pu2clr/Si4825_RADIO_HACK/Images/band_selector_prototype_01.jpg

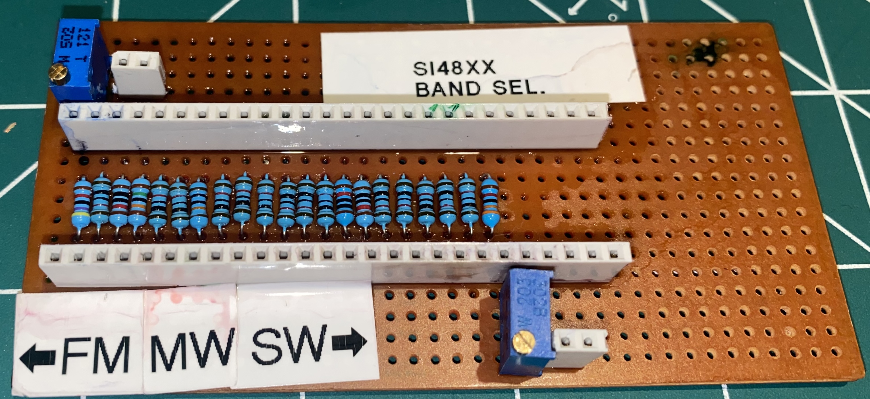
Images/band_selector_prototype_01.jpg
