pu2clr/Si4825_RADIO_HACK/Images/R_EXAMPLE_01.jpg

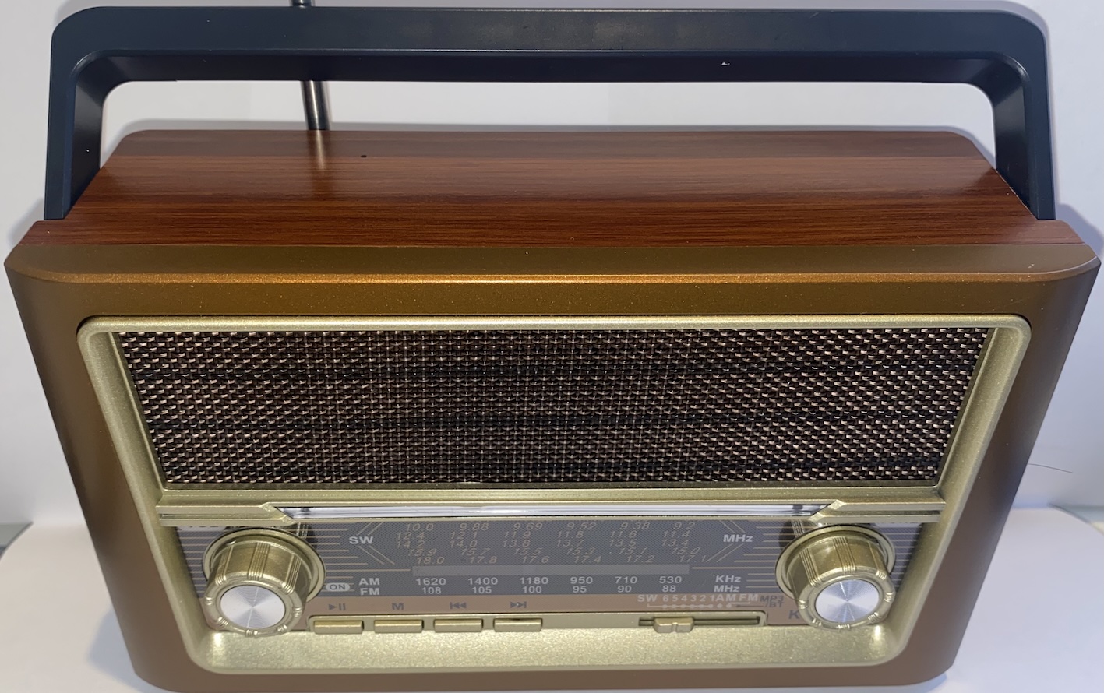
Images/R_EXAMPLE_01.jpg
