pu2clr/Si4825_RADIO_HACK/Images/R_EXAMPLE_02.jpg

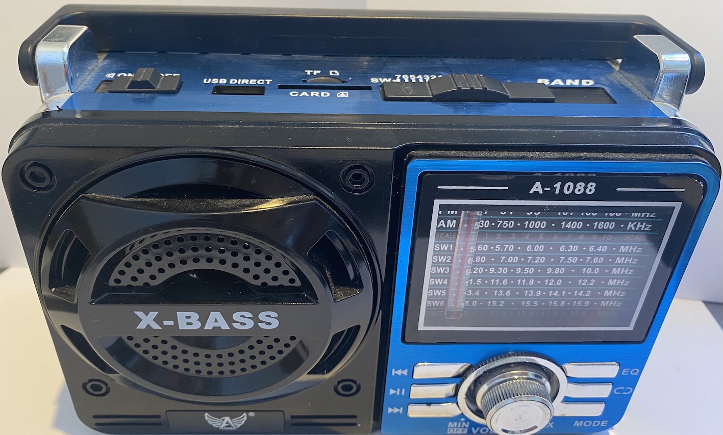
Images/R_EXAMPLE_02.jpg
