pu2clr/Si4825_RADIO_HACK/Images/SI4824A20.jpg

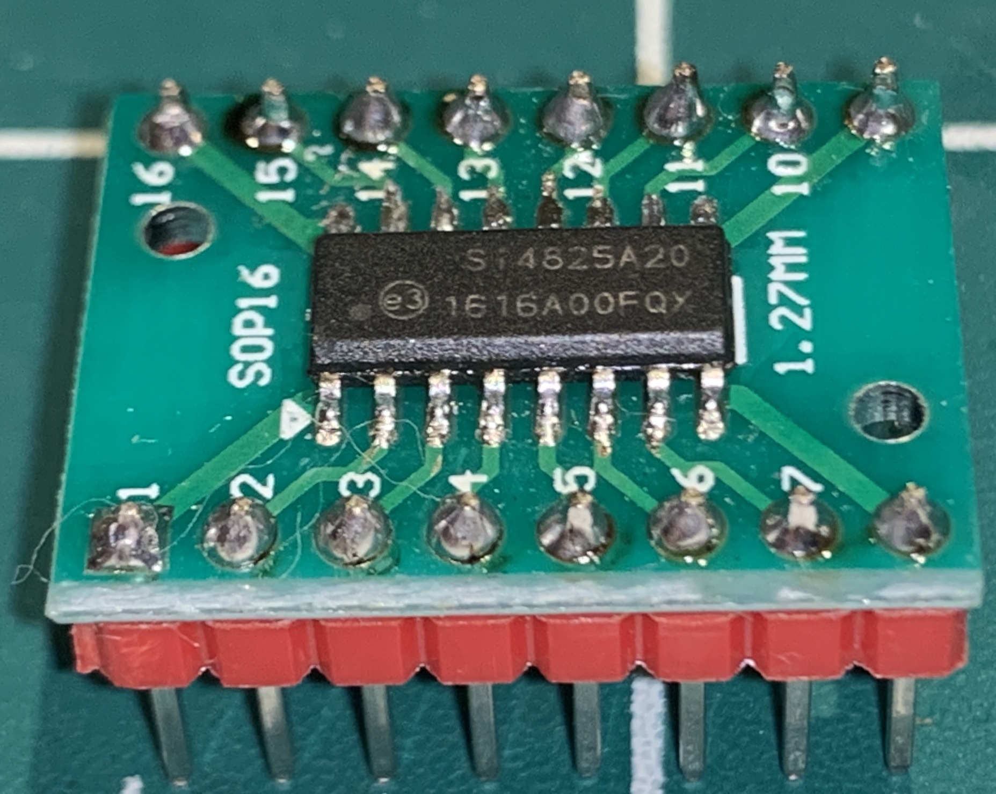
Images/SI4824A20.jpg
