pu2clr/Si4825_RADIO_HACK/schematic/SI4825_APP.jpg

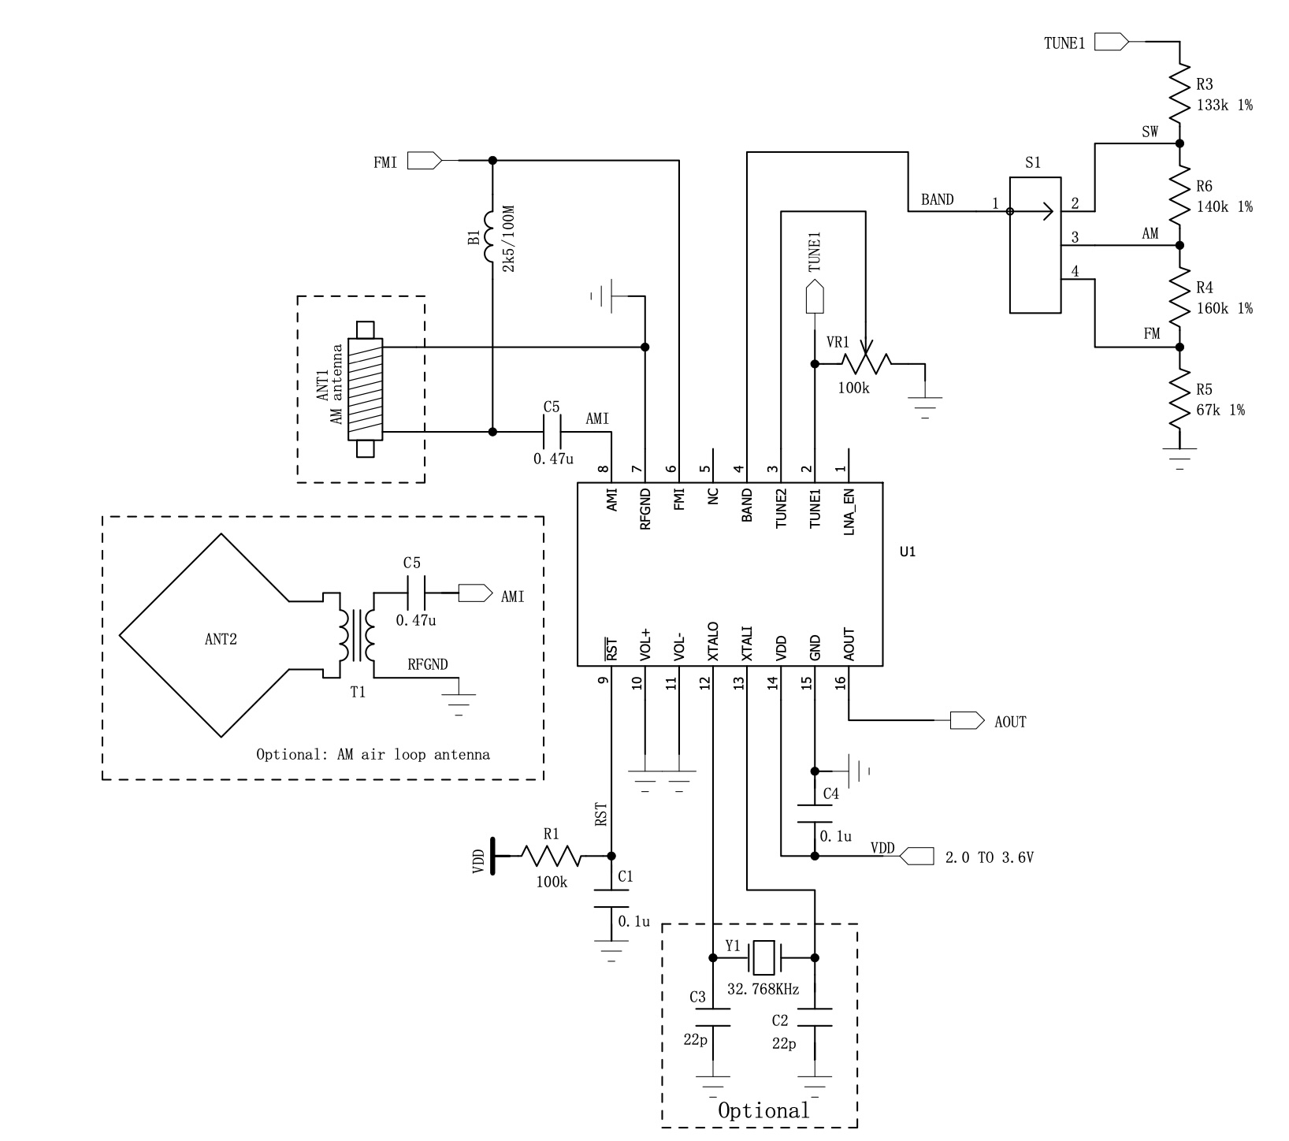
schematic/SI4825_APP.jpg
