pu2clr/Si4825_RADIO_HACK/schematic/SI4825_DIAG.jpg

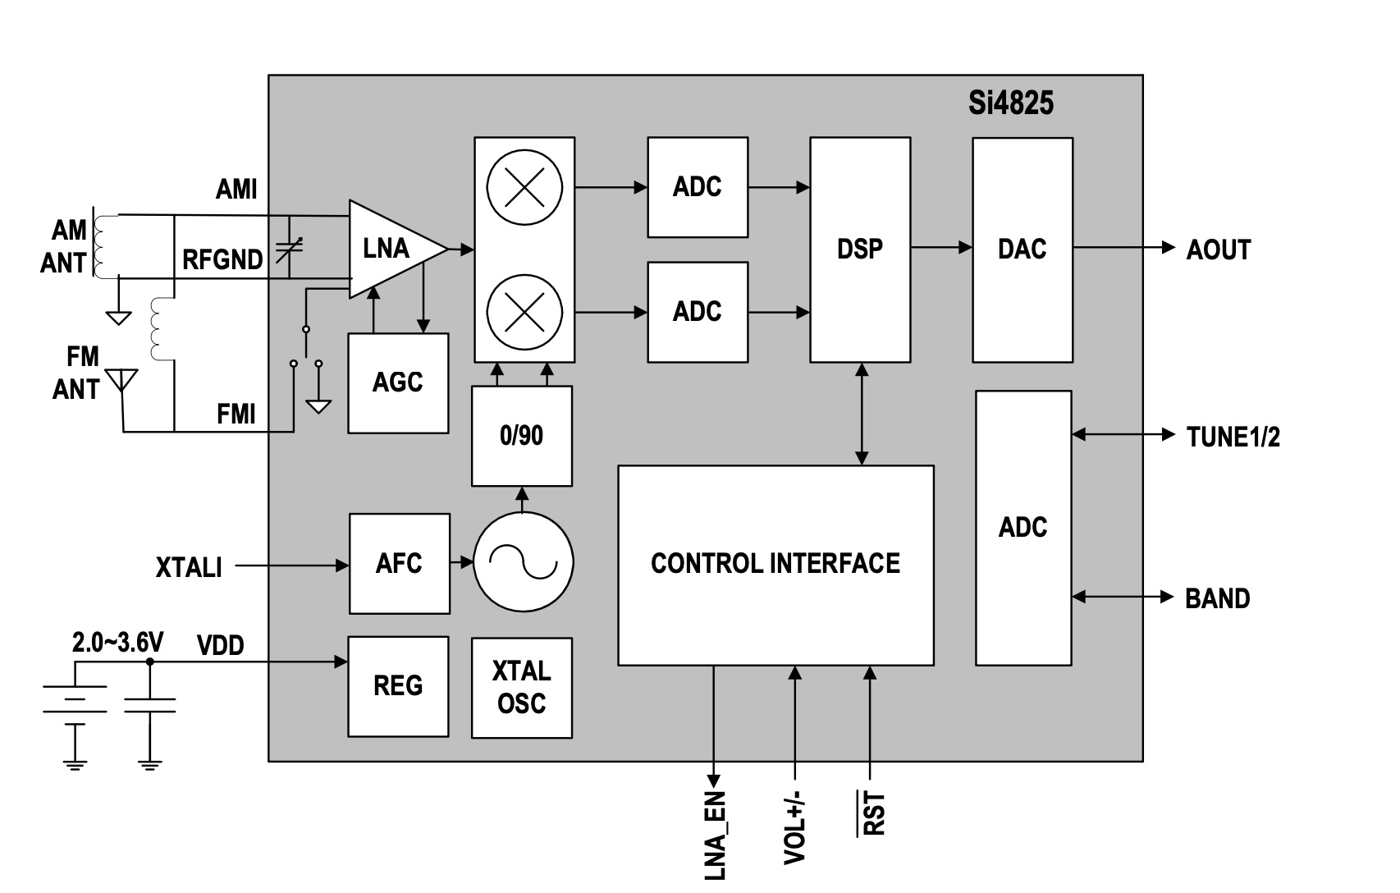
schematic/SI4825_DIAG.jpg
