pu2clr/Si4825_RADIO_HACK/Transformation/MOTOBRAS_RM_PFT73AC/Images/PCB_motobras_02.jpg

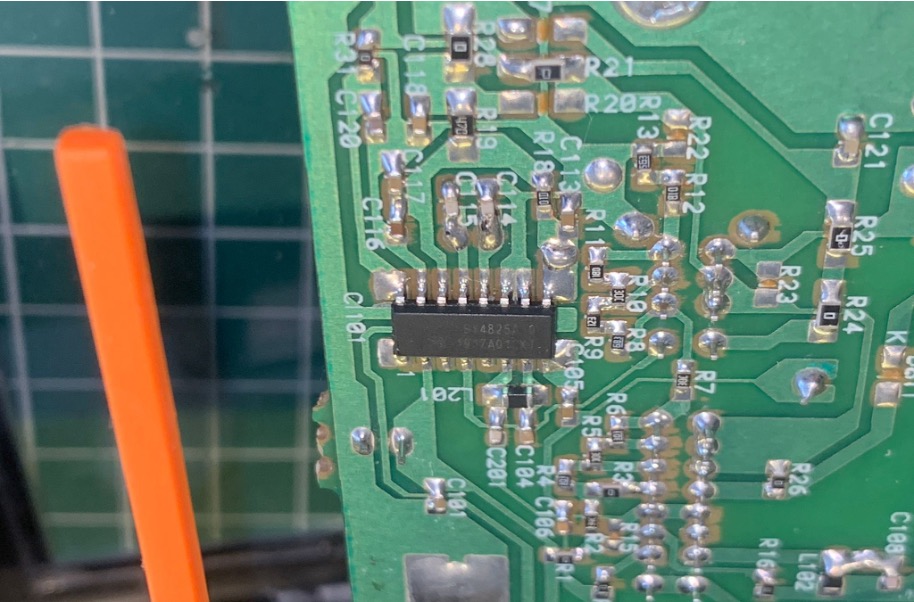
Transformation/MOTOBRAS_RM_PFT73AC/Images/PCB_motobras_02.jpg
