pu2clr/Si4825_RADIO_HACK/Transformation/MOTOBRAS_RM_PFT73AC/Images/Polia_01.jpg

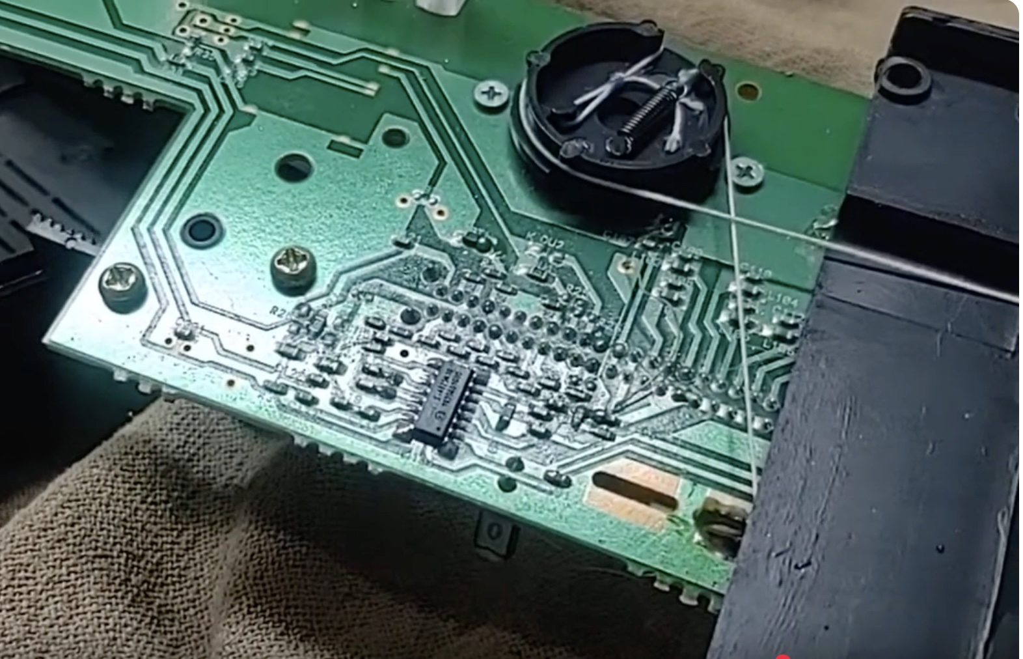
Transformation/MOTOBRAS_RM_PFT73AC/Images/Polia_01.jpg
