pu2clr/Si4825_RADIO_HACK/Transformation/MOTOBRAS_RM_PFT73AC/Images/R05_03.jpg

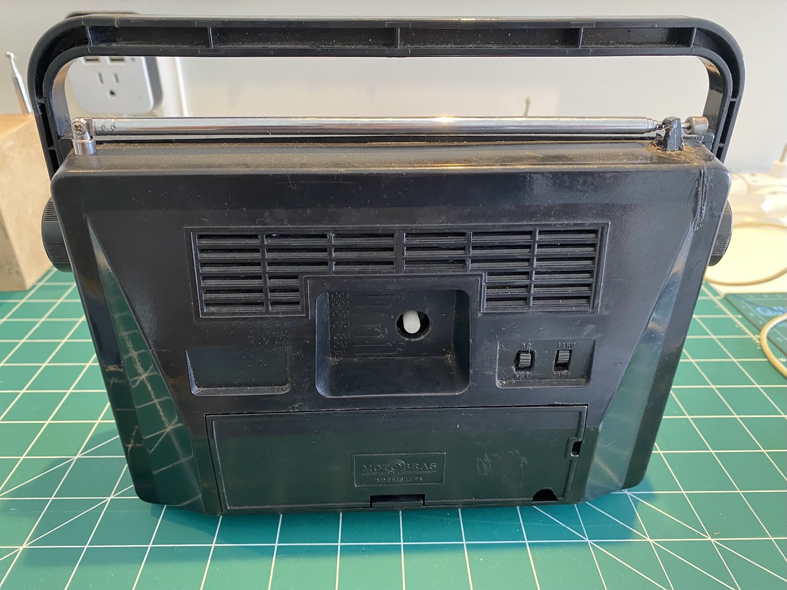
Transformation/MOTOBRAS_RM_PFT73AC/Images/R05_03.jpg
