pu2clr/Si4825_RADIO_HACK/Transformation/MOTOBRAS_RM_PFT73AC/Images/R08_01.jpeg

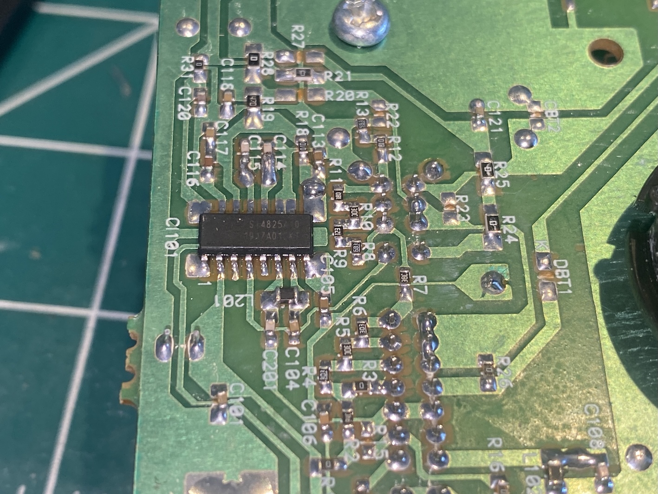
Transformation/MOTOBRAS_RM_PFT73AC/Images/R08_01.jpeg
