pu2clr/Si4825_RADIO_HACK/Images/prototype_si4825_tester_06.jpg

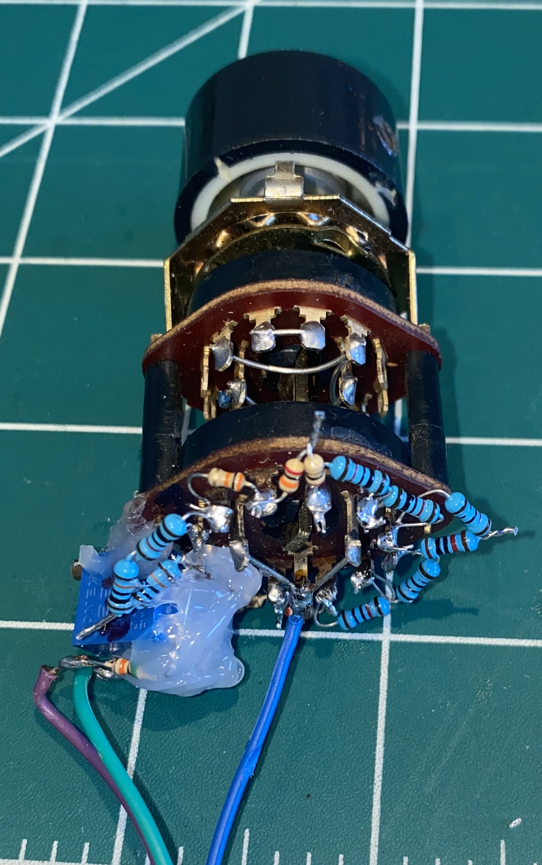
Images/prototype_si4825_tester_06.jpg
