pu2clr/Si4825_RADIO_HACK/schematic/Kicad/si4825_basic_setup/si4825_basic_setup.kicad_sch

## KiCad design schematic/Kicad/si4825_basic_setup/si4825_basic_setup.kicad_sch (2024-12-29)

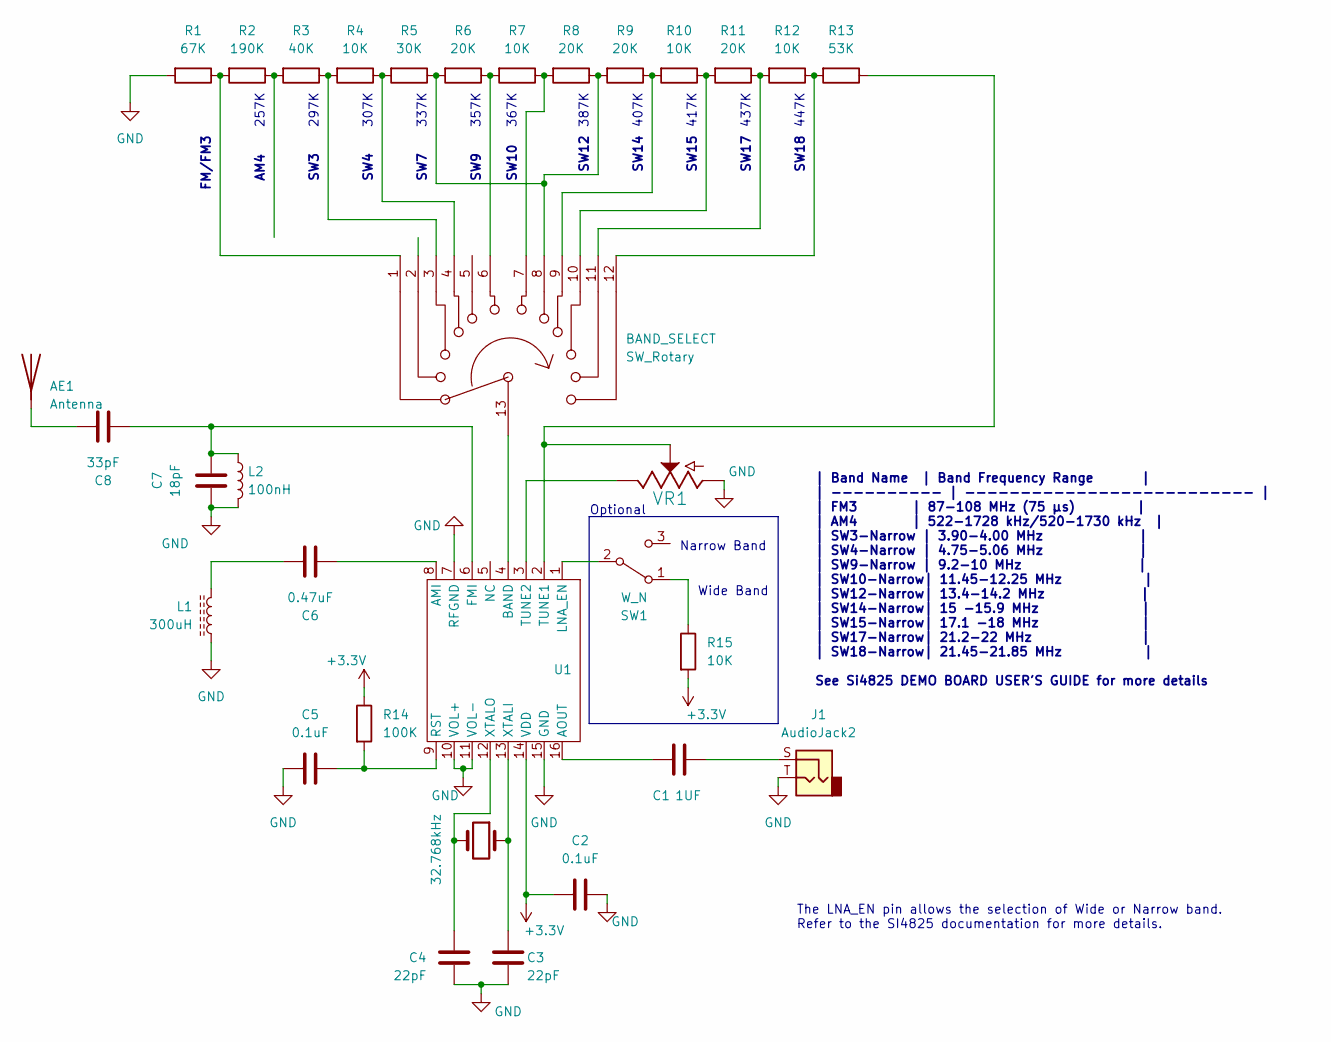
[picture p91: schematic si4825_basic_setup.kicad_sch]

Parts:
AE1: Antenna
BAND_SELECT: SW_Rotary
C1: 1UF
C2, C5: 0.1uF
C3, C4: 22pF
C6: 0.47uF
C7: 18pF
C8: 33pF
J1: AudioJack2
L1: 300uH
L2: 100nH
R1: 67K
R2: 190K
R3: 40K
R4, R7, R10, R12, R15: 10K
R5: 30K
R6, R8, R9, R11: 20K
R13: 53K
R14: 100K
SW1: W_N
U1: SI4825
VR1: 100K; POT-PTH-ALPS
Y1: 32.768kHz

Connections:
+3.3V: C2.2, R14.1, R15.2, U1.14 (VDD)
GND: C2.1, C3.2, C4.2, C5.2, C7.1, J1.T, L1.2, L2.2, R1.2, U1.7 (RFGND), U1.10 (VOL+), U1.11 (VOL-), U1.15 (GND), VR1.P$3 (A)
unnamed: AE1.1, C8.2
unnamed: BAND_SELECT.1, R1.1, R2.2
unnamed: BAND_SELECT.3, R3.1, R4.2
unnamed: BAND_SELECT.4, R4.1, R5.2
unnamed: BAND_SELECT.6, R6.1, R7.2
unnamed: BAND_SELECT.7, R7.1, R8.2
unnamed: BAND_SELECT.8, R5.1, R6.2, R8.1, R9.2
unnamed: BAND_SELECT.9, R9.1, R10.2
unnamed: BAND_SELECT.10, R10.1, R11.2
unnamed: BAND_SELECT.11, R11.1, R12.2
unnamed: BAND_SELECT.12, R12.1, R13.2
unnamed: BAND_SELECT.13, U1.4 (BAND)
unnamed: C1.1, J1.S
unnamed: C1.2, U1.16 (AOUT)
unnamed: C3.1, U1.13 (XTALI), Y1.1
unnamed: C4.1, U1.12 (XTALO), Y1.2
unnamed: C5.1, R14.2, U1.9 (RST)
unnamed: C6.1, U1.8 (AMI)
unnamed: C6.2, L1.1
unnamed: C7.2, C8.1, L2.1, U1.6 (FMI)
unnamed: R2.1, R3.2
unnamed: R13.1, U1.2 (TUNE1), VR1.P$2 (S)
unnamed: R15.1, SW1.1 (A)
unnamed: SW1.2 (B), U1.1 (LNA_EN)
unnamed: U1.3 (TUNE2), VR1.P$1 (E)

Notes on the sheet:
SW7
447K
Wide Band
437K
367K
337K
SW15
SW12
417K
SW9
SW18
AM4
297K
357K
407K
SW4
307K
The LNA_EN pin allows the selection of Wide or Narrow band. Refer to the SI4825 documentation for more details.
| Band Name | Band Frequency Range | | ---------- | -------------------------- | | FM3 | 87-108 MHz (75 µs) | | AM4 | 522-1728 kHz/520-1730 kHz | | SW3-Narrow | 3.90-4.00 MHz | | SW4-Narrow | 4.75-5.06 MHz | | SW9-Narrow | 9.2-10 MHz | | SW10-Narrow| 11.45-12.25 MHz | | SW12-Narrow| 13.4-14.2 MHz |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
Narrow Band
Optional
387K
SW17
257K
SW14
FM/FM3
SW3
SW10
